Cib0rg/macroboard/firmware/main/protocol/protocol_handler.c

/**
 * @file protocol_handler.c
 * @brief Protocol command handler implementation
 */

#include "common.h"
#include "protocol_handler.h"
#include "packet_parser.h"
#include "protocol_types.h"
#include "image_transfer.h"
#include "text_transfer.h"
#include "plugin_display.h"
#include "config.h"
#include "profile/profile_manager.h"
#include "storage/profile_storage.h"
#include "storage/image_storage.h"
#include "storage/save_task.h"
#include "usb/usb_vendor.h"
#include "esp_littlefs.h"
#include "esp_system.h"

static const char* TAG = "PROTOCOL";

QueueHandle_t protocol_cmd_queue = NULL;
static uint16_t response_sequence = 0;

// Forward declarations of command handlers
static esp_err_t handle_ping(const uint8_t* payload, uint16_t length, uint8_t* response, uint16_t* response_len);
static esp_err_t handle_get_device_info(const uint8_t* payload, uint16_t length, uint8_t* response, uint16_t* response_len);
static esp_err_t handle_set_profile(const uint8_t* payload, uint16_t length, uint8_t* response, uint16_t* response_len);
static esp_err_t handle_get_folder_state(const uint8_t* payload, uint16_t length, uint8_t* response, uint16_t* response_len);
static esp_err_t handle_start_image_transfer(const uint8_t* payload, uint16_t length, uint8_t* response, uint16_t* response_len);
static esp_err_t handle_image_data_chunk(const uint8_t* payload, uint16_t length, uint8_t* response, uint16_t* response_len);
static esp_err_t handle_end_image_transfer(const uint8_t* payload, uint16_t length, uint8_t* response, uint16_t* response_len);
static esp_err_t handle_get_button_image(const uint8_t* payload, uint16_t length, uint8_t* response, uint16_t* response_len);
static esp_err_t handle_get_image_hashes(const uint8_t* payload, uint16_t length, uint8_t* response, uint16_t* response_len);
static esp_err_t handle_clear_button_image(const uint8_t* payload, uint16_t length, uint8_t* response, uint16_t* response_len);
static esp_err_t handle_set_button_action(const uint8_t* payload, uint16_t length, uint8_t* response, uint16_t* response_len);
static esp_err_t handle_get_button_action(const uint8_t* payload, uint16_t length, uint8_t* response, uint16_t* response_len);
static esp_err_t handle_set_encoder_action(const uint8_t* payload, uint16_t length, uint8_t* response, uint16_t* response_len);
static esp_err_t handle_set_button_long_press_action(const uint8_t* payload, uint16_t length, uint8_t* response, uint16_t* response_len);
static esp_err_t handle_set_button_long_press_name(const uint8_t* payload, uint16_t length, uint8_t* response, uint16_t* response_len);
static esp_err_t handle_set_button_name(const uint8_t* payload, uint16_t length, uint8_t* response, uint16_t* response_len);
static esp_err_t handle_set_button_text_start(const uint8_t* payload, uint16_t length, uint8_t* response, uint16_t* response_len);
static esp_err_t handle_set_button_text_chunk(const uint8_t* payload, uint16_t length, uint8_t* response, uint16_t* response_len);
static esp_err_t handle_set_button_text_end(const uint8_t* payload, uint16_t length, uint8_t* response, uint16_t* response_len);
static esp_err_t handle_set_folder_button_action(const uint8_t* payload, uint16_t length, uint8_t* response, uint16_t* response_len);
static esp_err_t handle_set_folder_button_name(const uint8_t* payload, uint16_t length, uint8_t* response, uint16_t* response_len);
static esp_err_t handle_set_folder_button_led(const uint8_t* payload, uint16_t length, uint8_t* response, uint16_t* response_len);
static esp_err_t handle_set_led_color(const uint8_t* payload, uint16_t length, uint8_t* response, uint16_t* response_len);
static esp_err_t handle_get_led_color(const uint8_t* payload, uint16_t length, uint8_t* response, uint16_t* response_len);
static esp_err_t handle_set_backlight(const uint8_t* payload, uint16_t length, uint8_t* response, uint16_t* response_len);
static esp_err_t handle_save_profile(const uint8_t* payload, uint16_t length, uint8_t* response, uint16_t* response_len);
static esp_err_t handle_delete_profile(const uint8_t* payload, uint16_t length, uint8_t* response, uint16_t* response_len);
static esp_err_t handle_refresh_displays(const uint8_t* payload, uint16_t length, uint8_t* response, uint16_t* response_len);
static esp_err_t handle_factory_reset(const uint8_t* payload, uint16_t length, uint8_t* response, uint16_t* response_len);

// Command handler table
typedef struct {
    uint8_t command_id;
    command_handler_t handler;
} command_entry_t;

static const command_entry_t command_table[] = {
    {CMD_PING,            handle_ping},
    {CMD_GET_DEVICE_INFO, handle_get_device_info},
    {CMD_SET_PROFILE,     handle_set_profile},
    {CMD_GET_FOLDER_STATE, handle_get_folder_state},
    {CMD_START_IMAGE_TRANSFER, handle_start_image_transfer},
    {CMD_IMAGE_DATA_CHUNK, handle_image_data_chunk},
    {CMD_END_IMAGE_TRANSFER, handle_end_image_transfer},
    {CMD_GET_BUTTON_IMAGE, handle_get_button_image},
    {CMD_GET_IMAGE_HASHES, handle_get_image_hashes},
    {CMD_CLEAR_BUTTON_IMAGE, handle_clear_button_image},
    {CMD_SET_BUTTON_ACTION, handle_set_button_action},
    {CMD_SET_ENCODER_ACTION, handle_set_encoder_action},
    {CMD_SET_BUTTON_LONG_PRESS_ACTION, handle_set_button_long_press_action},
    {CMD_SET_BUTTON_LONG_PRESS_NAME,  handle_set_button_long_press_name},
    {CMD_GET_BUTTON_ACTION, handle_get_button_action},
    {CMD_SET_BUTTON_NAME,            handle_set_button_name},
    {CMD_SET_FOLDER_BUTTON_ACTION,              handle_set_folder_button_action},
    {CMD_SET_FOLDER_BUTTON_NAME,               handle_set_folder_button_name},
    {CMD_SET_FOLDER_BUTTON_LED,                handle_set_folder_button_led},
    {CMD_PLUGIN_DISPLAY,                       handle_plugin_display},
    {CMD_SET_LED_COLOR, handle_set_led_color},
    {CMD_GET_LED_COLOR, handle_get_led_color},
    {CMD_SET_BACKLIGHT, handle_set_backlight},
    {CMD_SAVE_PROFILE, handle_save_profile},
    {CMD_DELETE_PROFILE, handle_delete_profile},
    {CMD_REFRESH_DISPLAYS, handle_refresh_displays},
    {CMD_SET_BUTTON_TEXT_START, handle_set_button_text_start},
    {CMD_SET_BUTTON_TEXT_CHUNK, handle_set_button_text_chunk},
    {CMD_SET_BUTTON_TEXT_END,   handle_set_button_text_end},
    {CMD_FACTORY_RESET,         handle_factory_reset},
};

esp_err_t protocol_handler_init(void) {
    ESP_LOGI(TAG, "Initializing protocol handler");
    
    protocol_cmd_queue = xQueueCreate(32, sizeof(protocol_packet_t));
    if (protocol_cmd_queue == NULL) {
        ESP_LOGE(TAG, "Failed to create protocol command queue");
        return ESP_FAIL;
    }
    
    ESP_LOGI(TAG, "Protocol handler initialized");
    return ESP_OK;
}

esp_err_t protocol_handle_packet(const uint8_t* data, size_t length) {
    protocol_packet_t packet;
    
    esp_err_t ret = packet_parse(data, length, &packet);
    if (ret != ESP_OK) {
        ESP_LOGW(TAG, "Failed to parse packet: %s", esp_err_to_name(ret));
        return ret;
    }
    
    // Send to protocol task queue
    if (xQueueSend(protocol_cmd_queue, &packet, pdMS_TO_TICKS(100)) != pdTRUE) {
        ESP_LOGW(TAG, "Protocol queue full, dropping packet");
        return ESP_ERR_TIMEOUT;
    }
    
    return ESP_OK;
}

esp_err_t protocol_send_response(uint8_t command_id, const uint8_t* payload, uint16_t payload_len) {
    protocol_packet_t packet;
    
    esp_err_t ret = packet_build(command_id, payload, payload_len, response_sequence++, &packet);
    if (ret != ESP_OK) {
        return ret;
    }
    
    return usb_vendor_send((uint8_t*)&packet, sizeof(packet));
}

esp_err_t protocol_send_event(uint8_t event_id, const uint8_t* payload, uint16_t payload_len) {
    return protocol_send_response(event_id, payload, payload_len);
}

void protocol_task(void* arg) {
    (void)arg;
    protocol_packet_t packet;
    uint8_t response_payload[PROTOCOL_PAYLOAD_SIZE];
    uint16_t response_len;
    
    ESP_LOGI(TAG, "Protocol task started");
    
    while (1) {
        if (xQueueReceive(protocol_cmd_queue, &packet, portMAX_DELAY)) {
            ESP_LOGI(TAG, "Processing command 0x%02X", packet.command_id);
            
            // Find command handler
            command_handler_t handler = NULL;
            for (int i = 0; i < sizeof(command_table) / sizeof(command_entry_t); i++) {
                if (command_table[i].command_id == packet.command_id) {
                    handler = command_table[i].handler;
                    break;
                }
            }
            
            if (handler != NULL) {
                // Execute handler
                response_len = 0;
                esp_err_t ret = handler(packet.payload, packet.payload_length,
                                        response_payload, &response_len);

                if (ret == ESP_OK) {
                    // response_len == 0 means "no response" (e.g. streaming image chunks)
                    if (response_len > 0) {
                        protocol_send_response(packet.command_id, response_payload, response_len);
                    }
                } else if (response_len > 0) {
                    // Send error response (only when handler expected to reply)
                    response_payload[0] = STATUS_ERROR;
                    protocol_send_response(packet.command_id, response_payload, 1);
                }
            } else {
                ESP_LOGW(TAG, "Unknown command: 0x%02X", packet.command_id);
                response_payload[0] = STATUS_ERROR;
                protocol_send_response(packet.command_id, response_payload, 1);
            }
        }
    }
}

// Command handler implementations

static esp_err_t handle_ping(const uint8_t* payload, uint16_t length, 
                              uint8_t* response, uint16_t* response_len) {
    // Response: firmware version + uptime + current profile
    response[0] = FIRMWARE_VERSION_MAJOR;
    response[1] = FIRMWARE_VERSION_MINOR;
    response[2] = FIRMWARE_VERSION_PATCH;
    response[3] = 0; // Build number
    
    uint32_t uptime = esp_timer_get_time() / 1000000; // seconds
    memcpy(&response[4], &uptime, 4);
    
    response[8] = 0;
    
    *response_len = 9;
    return ESP_OK;
}

static esp_err_t handle_get_device_info(const uint8_t* payload, uint16_t length,
                                         uint8_t* response, uint16_t* response_len) {
    // Device ID (UUID) - for now use MAC address
    uint8_t mac[6];
    esp_efuse_mac_get_default(mac);
    memcpy(&response[0], mac, 6);
    memset(&response[6], 0, 10); // Pad to 16 bytes
    
    // Firmware version
    response[16] = FIRMWARE_VERSION_MAJOR;
    response[17] = FIRMWARE_VERSION_MINOR;
    response[18] = FIRMWARE_VERSION_PATCH;
    response[19] = 0;
    
    // Device capabilities
    response[20] = NUM_BUTTONS;
    response[21] = profile_storage_exists(0) ? 1 : 0;
    response[22] = 0;
    
    // Free flash space from LittleFS
    size_t total = 0, used = 0;
    esp_littlefs_info("storage", &total, &used);
    uint32_t free_space = (uint32_t)(total - used);
    memcpy(&response[23], &free_space, 4);
    
    // Image deduplication stats
    uint16_t unique_images = 0, total_mappings = 0;
    uint32_t saved_bytes = 0;
    image_storage_get_stats(&unique_images, &total_mappings, &saved_bytes);
    memcpy(&response[27], &unique_images, 2);
    memcpy(&response[29], &total_mappings, 2);
    memcpy(&response[31], &saved_bytes, 4);
    
    *response_len = 35;
    return ESP_OK;
}

// Device operates on a single profile slot; always acknowledge.
static esp_err_t handle_set_profile(const uint8_t* payload, uint16_t length,
                                     uint8_t* response, uint16_t* response_len) {
    response[0] = STATUS_OK;
    *response_len = 1;
    return ESP_OK;
}

static esp_err_t handle_get_folder_state(const uint8_t* payload, uint16_t length,
                                          uint8_t* response, uint16_t* response_len) {
    uint8_t folder_id = profile_get_current_folder(); // 0xFF if at root
    uint8_t depth     = profile_is_in_folder() ? 1 : 0; // simplified: 0=root, 1=in folder
    response[0] = STATUS_OK;
    response[1] = folder_id;
    response[2] = depth;
    *response_len = 3;
    return ESP_OK;
}

static esp_err_t handle_start_image_transfer(const uint8_t* payload, uint16_t length,
                                               uint8_t* response, uint16_t* response_len) {
    if (length < 11) {
        return ESP_ERR_INVALID_ARG;
    }

    uint8_t button_id = payload[1];
    uint32_t image_size;
    memcpy(&image_size, &payload[2], 4);
    uint8_t format    = payload[6];
    // payload[7]: transfer flags (TRANSFER_FLAG_VOLATILE etc.).
    // Old C# sends 160 here (width hint, ignored by firmware) — bit 0 = 0, so NOT volatile.
    // New C# sends explicit flags (0x00 = normal, 0x01 = volatile / no SPIFFS).
    uint8_t flags     = payload[7];
    // Byte 11 (optional): folder_id. 0xFF or absent means root button.
    uint8_t folder_id = (length >= 12) ? payload[11] : 0xFF;

    esp_err_t ret = image_transfer_start(0, folder_id, button_id, image_size, format, flags);

    response[0] = (ret == ESP_OK) ? STATUS_OK : STATUS_ERROR;
    uint16_t transfer_id = button_id;
    memcpy(&response[1], &transfer_id, 2);
    uint16_t max_chunk = 52;
    memcpy(&response[3], &max_chunk, 2);
    
    *response_len = 5;
    return ESP_OK;
}

static esp_err_t handle_image_data_chunk(const uint8_t* payload, uint16_t length,
                                          uint8_t* response, uint16_t* response_len) {
    // Compact streaming layout: [tid u8][chunkNum u16 LE][dataLen u8][data…]
    if (length < 4) {
        return ESP_ERR_INVALID_ARG;
    }

    // payload[0] = transfer_id (u8, ignored — single transfer at a time)
    uint16_t chunk_num;
    memcpy(&chunk_num, &payload[1], 2);
    uint16_t chunk_size = payload[3];  // u8 → u16

    esp_err_t ret = image_transfer_chunk(&payload[4], chunk_size, chunk_num);

    // No per-chunk ACK — streaming mode. On error the END handler will catch it via CRC.
    *response_len = 0;
    return ret;
}

static esp_err_t handle_end_image_transfer(const uint8_t* payload, uint16_t length,
                                            uint8_t* response, uint16_t* response_len) {
    // Compact END layout: [tid u8][totalChunks u32 LE][crc32 u32 LE] = 9 bytes
    if (length < 9) {
        return ESP_ERR_INVALID_ARG;
    }

    uint32_t expected_crc;
    memcpy(&expected_crc, &payload[5], 4);  // was at [6] with u16 tid
    
    uint32_t calculated_crc;
    esp_err_t ret = image_transfer_end(&calculated_crc);
    
    response[0] = (ret == ESP_OK && calculated_crc == expected_crc) ? STATUS_OK : STATUS_ERROR;
    memcpy(&response[1], &calculated_crc, 4);
    
    *response_len = 5;
    return ESP_OK;
}

static esp_err_t handle_set_button_action(const uint8_t* payload, uint16_t length,
                                           uint8_t* response, uint16_t* response_len) {
    if (length < 5) {
        return ESP_ERR_INVALID_ARG;
    }
    
    uint8_t button_id = payload[1];
    uint8_t action_type = payload[2];
    uint16_t action_len;
    memcpy(&action_len, &payload[3], 2);

    esp_err_t ret = profile_set_button_action(button_id, action_type,
                                               &payload[5], action_len);
    
    response[0] = (ret == ESP_OK) ? STATUS_OK : STATUS_ERROR;
    *response_len = 1;

    return ESP_OK;
}

static esp_err_t handle_set_encoder_action(const uint8_t* payload, uint16_t length,
                                            uint8_t* response, uint16_t* response_len) {
    // Payload: [slot (1)] [action_type (1)] [action_data_len (2 LE)] [action_data ...]
    // Slots: 0=CW, 1=CCW, 2=press short, 3=press long
    if (length < 4) {
        response[0] = STATUS_ERROR;
        *response_len = 1;
        return ESP_OK;
    }

    uint8_t slot = payload[0];
    uint8_t action_type = payload[1];
    uint16_t action_len;
    memcpy(&action_len, &payload[2], 2);

    if (action_len > PROTOCOL_PAYLOAD_SIZE - 4) action_len = PROTOCOL_PAYLOAD_SIZE - 4;

    esp_err_t ret = profile_set_encoder_action(slot, action_type,
                                               length > 4 ? &payload[4] : NULL, action_len);
    response[0] = (ret == ESP_OK) ? STATUS_OK : STATUS_ERROR;
    *response_len = 1;
    return ESP_OK;
}

static esp_err_t handle_set_button_long_press_action(const uint8_t* payload, uint16_t length,
                                                      uint8_t* response, uint16_t* response_len) {
    // Payload: [profile_id(1)][folder_id(1)][button_id(1)][action_type(1)][data_len(2 LE)][data...]
    // folder_id=0xFF → root buttons
    if (length < 6) { response[0] = STATUS_ERROR; *response_len = 1; return ESP_OK; }
    uint8_t folder_id   = payload[1];
    uint8_t button_id   = payload[2];
    uint8_t action_type = payload[3];
    uint16_t action_len; memcpy(&action_len, &payload[4], 2);
    if (action_len > PROTOCOL_PAYLOAD_SIZE - 6) action_len = PROTOCOL_PAYLOAD_SIZE - 6;
    esp_err_t ret = profile_set_button_long_press_action(button_id, folder_id, action_type,
                                                          length > 6 ? &payload[6] : NULL, action_len);
    response[0] = (ret == ESP_OK) ? STATUS_OK : STATUS_ERROR;
    *response_len = 1;
    return ESP_OK;
}

static esp_err_t handle_set_button_long_press_name(const uint8_t* payload, uint16_t length,
                                                     uint8_t* response, uint16_t* response_len) {
    // Payload: [profile_id(1)][folder_id(1)][button_id(1)][name (UTF-8, no null needed)]
    // folder_id=0xFF → root buttons
    if (length < 3) { response[0] = STATUS_ERROR; *response_len = 1; return ESP_OK; }
    uint8_t folder_id = payload[1];
    uint8_t button_id = payload[2];
    char name[BUTTON_NAME_MAX_LEN];
    memset(name, 0, sizeof(name));
    uint16_t name_len = length - 3;
    if (name_len >= BUTTON_NAME_MAX_LEN) name_len = BUTTON_NAME_MAX_LEN - 1;
    if (name_len > 0) memcpy(name, &payload[3], name_len);
    esp_err_t ret = profile_set_button_long_press_name(button_id, folder_id, name);
    response[0] = (ret == ESP_OK) ? STATUS_OK : STATUS_ERROR;
    *response_len = 1;
    return ESP_OK;
}

static esp_err_t handle_set_button_name(const uint8_t* payload, uint16_t length,
                                         uint8_t* response, uint16_t* response_len) {
    // payload: [profile_id][button_id][name (UTF-8, null-terminated, max 32 bytes)]
    if (length < 2) {
        response[0] = STATUS_ERROR;
        *response_len = 1;
        return ESP_OK;
    }

    uint8_t button_id = payload[1];

    char name[BUTTON_NAME_MAX_LEN];
    memset(name, 0, sizeof(name));

    uint16_t name_len = length - 2;
    if (name_len >= BUTTON_NAME_MAX_LEN) name_len = BUTTON_NAME_MAX_LEN - 1;
    if (name_len > 0) memcpy(name, &payload[2], name_len);

    esp_err_t ret = profile_set_button_name(button_id, name);
    response[0] = (ret == ESP_OK) ? STATUS_OK : STATUS_ERROR;
    *response_len = 1;
    return ESP_OK;
}

static esp_err_t handle_set_folder_button_action(const uint8_t* payload, uint16_t length,
                                                   uint8_t* response, uint16_t* response_len) {
    // payload: [profile_id][folder_id][button_id][action_type][action_len_lo][action_len_hi][action_data...]
    if (length < 6) { response[0] = STATUS_ERROR; *response_len = 1; return ESP_OK; }
    uint8_t folder_id   = payload[1];
    uint8_t button_id   = payload[2];
    uint8_t action_type = payload[3];
    uint16_t action_len; memcpy(&action_len, &payload[4], 2);
    esp_err_t ret = profile_set_folder_button_action(folder_id, button_id,
                                                      action_type, &payload[6], action_len);
    response[0] = (ret == ESP_OK) ? STATUS_OK : STATUS_ERROR;
    *response_len = 1;
    return ESP_OK;
}

static esp_err_t handle_set_folder_button_name(const uint8_t* payload, uint16_t length,
                                                uint8_t* response, uint16_t* response_len) {
    // payload: [profile_id][folder_id][button_id][name (null-term, up to BUTTON_NAME_MAX_LEN)]
    if (length < 3) { response[0] = STATUS_ERROR; *response_len = 1; return ESP_OK; }
    uint8_t folder_id = payload[1];
    uint8_t button_id = payload[2];
    char name[BUTTON_NAME_MAX_LEN];
    memset(name, 0, sizeof(name));
    uint16_t name_len = length - 3;
    if (name_len >= BUTTON_NAME_MAX_LEN) name_len = BUTTON_NAME_MAX_LEN - 1;
    if (name_len > 0) memcpy(name, &payload[3], name_len);
    esp_err_t ret = profile_set_folder_button_name(folder_id, button_id, name);
    response[0] = (ret == ESP_OK) ? STATUS_OK : STATUS_ERROR;
    *response_len = 1;
    return ESP_OK;
}

static esp_err_t handle_set_folder_button_led(const uint8_t* payload, uint16_t length,
                                               uint8_t* response, uint16_t* response_len) {
    // payload: [profile_id][folder_id][button_id][r][g][b][brightness][effect]
    if (length < 8) { response[0] = STATUS_ERROR; *response_len = 1; return ESP_OK; }
    esp_err_t ret = profile_set_folder_button_led(
        payload[1], payload[2],
        payload[3], payload[4], payload[5], payload[6], payload[7]);
    response[0] = (ret == ESP_OK) ? STATUS_OK : STATUS_ERROR;
    *response_len = 1;
    return ESP_OK;
}


static esp_err_t handle_set_led_color(const uint8_t* payload, uint16_t length,
                                       uint8_t* response, uint16_t* response_len) {
    if (length < 7) {
        return ESP_ERR_INVALID_ARG;
    }
    
    uint8_t button_id = payload[1];
    uint8_t r = payload[2];
    uint8_t g = payload[3];
    uint8_t b = payload[4];
    uint8_t brightness = payload[5];
    uint8_t effect = payload[6];

    esp_err_t ret = profile_set_led_color(button_id, r, g, b, brightness, effect);
    
    response[0] = (ret == ESP_OK) ? STATUS_OK : STATUS_ERROR;
    *response_len = 1;
    
    return ESP_OK;
}

static esp_err_t handle_set_backlight(const uint8_t* payload, uint16_t length,
                                       uint8_t* response, uint16_t* response_len) {
    if (length < 1) {
        return ESP_ERR_INVALID_ARG;
    }
    
    extern esp_err_t gc9a01_set_brightness(uint8_t brightness);
    extern esp_err_t gc9a01_set_backlight(bool enabled);
    extern uint8_t gc9a01_get_brightness(void);
    
    esp_err_t ret;
    
    if (length >= 2) {
        // New format: payload[0] = enabled, payload[1] = brightness (0-255)
        uint8_t brightness = payload[1];
        if (payload[0] == 0) {
            brightness = 0;  // Force off
        }
        ret = gc9a01_set_brightness(brightness);
    } else {
        // Legacy format: payload[0] = enabled (on/off only)
        uint8_t enabled = payload[0];
        ret = gc9a01_set_backlight(enabled != 0);
    }
    
    response[0] = (ret == ESP_OK) ? STATUS_OK : STATUS_ERROR;
    response[1] = gc9a01_get_brightness();
    *response_len = 2;
    
    return ESP_OK;
}

static esp_err_t handle_save_profile(const uint8_t* payload, uint16_t length,
                                      uint8_t* response, uint16_t* response_len) {
    (void)payload; (void)length;

    // Ensure all async SPIFFS image writes are complete before persisting the
    // profile.  Without this, image_size fields could be stale in the saved binary.
    save_task_drain();

    esp_err_t ret = profile_save_to_storage();

    if (ret == ESP_OK) {
        image_storage_gc(profile_get());
    }

    response[0] = (ret == ESP_OK) ? STATUS_OK : STATUS_ERROR;
    // Bytes written = size of profile_t structure
    uint32_t bytes_written = (ret == ESP_OK) ? sizeof(profile_t) : 0;
    memcpy(&response[1], &bytes_written, 4);

    *response_len = 5;
    return ESP_OK;
}

static esp_err_t handle_delete_profile(const uint8_t* payload, uint16_t length,
                                        uint8_t* response, uint16_t* response_len) {
    // Device holds only one profile (slot 0) — deletion is a no-op.
    response[0] = STATUS_OK;
    *response_len = 1;
    return ESP_OK;
}

static esp_err_t handle_refresh_displays(const uint8_t* payload, uint16_t length,
                                          uint8_t* response, uint16_t* response_len) {
    profile_refresh_displays();
    response[0] = STATUS_OK;
    *response_len = 1;
    return ESP_OK;
}

static esp_err_t handle_get_button_action(const uint8_t* payload, uint16_t length,
                                           uint8_t* response, uint16_t* response_len) {
    if (length < 2) {
        return ESP_ERR_INVALID_ARG;
    }
    
    uint8_t button_id = payload[1];

    profile_t* profile = profile_get();
    if (button_id >= NUM_BUTTONS) {
        response[0] = STATUS_ERROR;
        *response_len = 1;
        return ESP_OK;
    }

    button_config_t* button = &profile->buttons[button_id];

    // Response format: status + action_type + action_len (2 bytes) + action_data
    response[0] = STATUS_OK;
    response[1] = button->action_type;
    memcpy(&response[2], &button->action_data_len, 2);
    
    uint16_t copy_len = button->action_data_len;
    if (copy_len > PROTOCOL_PAYLOAD_SIZE - 4) {
        copy_len = PROTOCOL_PAYLOAD_SIZE - 4;
    }
    
    memcpy(&response[4], button->action_data, copy_len);
    *response_len = 4 + copy_len;
    
    return ESP_OK;
}

static esp_err_t handle_get_led_color(const uint8_t* payload, uint16_t length,
                                       uint8_t* response, uint16_t* response_len) {
    if (length < 2) {
        return ESP_ERR_INVALID_ARG;
    }
    
    uint8_t button_id = payload[1];

    profile_t* profile = profile_get();
    if (button_id >= NUM_BUTTONS) {
        response[0] = STATUS_ERROR;
        *response_len = 1;
        return ESP_OK;
    }

    button_config_t* button = &profile->buttons[button_id];

    // Response format: status + r + g + b + brightness + effect
    response[0] = STATUS_OK;
    response[1] = button->led_r;
    response[2] = button->led_g;
    response[3] = button->led_b;
    response[4] = button->led_brightness;
    response[5] = button->led_effect;
    *response_len = 6;
    
    return ESP_OK;
}

static esp_err_t handle_get_button_image(const uint8_t* payload, uint16_t length,
                                          uint8_t* response, uint16_t* response_len) {
    if (length < 2) {
        return ESP_ERR_INVALID_ARG;
    }

    uint8_t button_id = payload[1];

    profile_t* profile = profile_get();
    if (button_id >= NUM_BUTTONS) {
        response[0] = STATUS_ERROR;
        *response_len = 1;
        return ESP_OK;
    }

    button_config_t* button = &profile->buttons[button_id];

    // Response format: status + image_offset (4 bytes) + image_size (4 bytes) + image_format
    response[0] = STATUS_OK;
    memcpy(&response[1], &button->image_offset, 4);
    memcpy(&response[5], &button->image_size, 4);
    response[9] = button->image_format;
    *response_len = 10;

    return ESP_OK;
}

// Text transfer handlers — CMD 0x38 / 0x39 / 0x3A

static esp_err_t handle_set_button_text_start(const uint8_t* payload, uint16_t length,
                                               uint8_t* response, uint16_t* response_len) {
    // Payload: [profile_id(1)][folder_id(1)][button_id(1)][action_slot(1)][step_index(1)][data_size(4 LE)]
    if (length < 9) { response[0] = STATUS_ERROR; *response_len = 1; return ESP_OK; }
    uint8_t  profile_id  = payload[0];
    uint8_t  folder_id   = payload[1];
    uint8_t  button_id   = payload[2];
    uint8_t  action_slot = payload[3];  // TEXT_ACTION_SHORT / TEXT_ACTION_LONG
    uint8_t  step_index  = payload[4];  // TEXT_STEP_DIRECT / TEXT_STEP_SEQ_BLOB / 0..15
    uint32_t data_size;
    memcpy(&data_size, &payload[5], 4);
    esp_err_t ret = text_transfer_start(profile_id, folder_id, button_id,
                                        action_slot, step_index, data_size);
    response[0] = (ret == ESP_OK) ? STATUS_OK : STATUS_ERROR;
    uint16_t max_chunk = 54; // PayloadSize(56) - chunkNum(2)
    memcpy(&response[1], &max_chunk, 2);
    *response_len = 3;
    return ESP_OK;
}

static esp_err_t handle_set_button_text_chunk(const uint8_t* payload, uint16_t length,
                                               uint8_t* response, uint16_t* response_len) {
    // Payload: [chunk_num(2 LE)][data...]
    if (length < 2) { response[0] = STATUS_ERROR; *response_len = 1; return ESP_OK; }
    uint16_t chunk_num;
    memcpy(&chunk_num, &payload[0], 2);
    uint16_t data_len = length - 2;
    esp_err_t ret = text_transfer_chunk(&payload[2], data_len, chunk_num);
    response[0] = (ret == ESP_OK) ? STATUS_OK : STATUS_ERROR;
    uint16_t next_chunk = chunk_num + 1;
    memcpy(&response[1], &next_chunk, 2);
    *response_len = 3;
    return ESP_OK;
}

static esp_err_t handle_set_button_text_end(const uint8_t* payload, uint16_t length,
                                             uint8_t* response, uint16_t* response_len) {
    (void)payload; (void)length;
    esp_err_t ret = text_transfer_end();
    response[0] = (ret == ESP_OK) ? STATUS_OK : STATUS_ERROR;
    *response_len = 1;
    return ESP_OK;
}

// Response: [status(1)][count(1)][{button_id(1), crc32_le(4)} × count]
static esp_err_t handle_get_image_hashes(const uint8_t* payload, uint16_t length,
                                          uint8_t* response, uint16_t* response_len) {
    (void)payload; (void)length;
    uint8_t count = 0;
    response[0] = STATUS_OK;
    for (uint8_t b = 0; b < NUM_BUTTONS; b++) {
        uint32_t crc;
        if (image_storage_get_crc(0, b, &crc) != ESP_OK) continue;
        int offset = 2 + count * 5;
        if (offset + 5 > PROTOCOL_PAYLOAD_SIZE) break;
        response[offset]     = b;
        response[offset + 1] = (uint8_t)(crc & 0xFF);
        response[offset + 2] = (uint8_t)((crc >> 8)  & 0xFF);
        response[offset + 3] = (uint8_t)((crc >> 16) & 0xFF);
        response[offset + 4] = (uint8_t)((crc >> 24) & 0xFF);
        count++;
    }
    response[1] = count;
    *response_len = 2 + (uint16_t)count * 5;
    ESP_LOGI(TAG, "GET_IMAGE_HASHES: %d entries", count);
    return ESP_OK;
}

// payload: [profile_id][button_id]
// Clears the stored image for a root button (sets image_size = 0) and refreshes the display
// so the button falls back to text rendering via profile_update_button_display.
static esp_err_t handle_clear_button_image(const uint8_t* payload, uint16_t length,
                                            uint8_t* response, uint16_t* response_len) {
    if (length < 2) {
        response[0] = STATUS_ERROR;
        *response_len = 1;
        return ESP_OK;
    }

    uint8_t button_id  = payload[1];

    if (button_id >= NUM_BUTTONS) {
        response[0] = STATUS_ERROR;
        *response_len = 1;
        return ESP_OK;
    }

    profile_t* prof = profile_get();

    prof->buttons[button_id].image_size = 0;
    profile_image_cache_invalidate(button_id, false);
    // Release the stored image blob (decrement refcount, delete if unreferenced).
    // Without this, the SPIFFS file stays allocated until the next image_storage_gc().
    image_storage_delete(0, button_id);
    profile_refresh_button_display(button_id);

    ESP_LOGI(TAG, "Cleared image for button=%d", button_id);
    response[0] = STATUS_OK;
    *response_len = 1;
    return ESP_OK;
}

static esp_err_t handle_factory_reset(const uint8_t* payload, uint16_t length,
                                      uint8_t* response, uint16_t* response_len) {
    ESP_LOGW(TAG, "Reboot requested via CMD_FACTORY_RESET — restarting in 100 ms");
    response[0] = STATUS_OK;
    *response_len = 1;
    // Small delay so the ACK packet can be flushed before we disappear
    vTaskDelay(pdMS_TO_TICKS(100));
    esp_restart();
    return ESP_OK; // unreachable
}
